bmc-labs/usb-can/pictures/usb-can_04.png

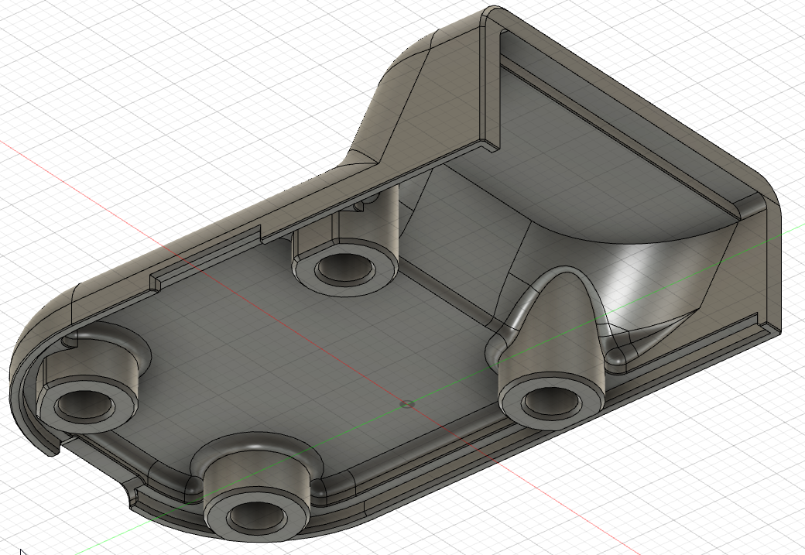
pictures/usb-can_04.png
